Ratatouille-Whiskers/OpenWhisker/Code/TED_MLX90393/TED_MLX90393.ino

#include <MLX90393.h>
#include <Wire.h>

#define DRDY_pin 5

MLX90393 mlx;
MLX90393::txyzRaw rawData;
MLX90393::txyz data;

bool dataReady = false;

// Max reading rate is 385hz @ i2c_clk=100kHz (Teensy 4.0)
// Max reading rate is 320hz @ i2c_clk=100kHz (Esp32)
// Max reading rate is 570hz @ i2c_clk=400kHz (Teensy 4.0)
// Max reading rate is hz @ i2c_clk=400kHz (Esp32)
// const byte axisFlags = MLX90393::X_FLAG | MLX90393::Y_FLAG | MLX90393::Z_FLAG; 
// Removing the z-axis from the reading increases 385hz -> 460hz @ i2c_clk=100kHz (Teensy 4.0)
// Removing the z-axis from the reading increases 320hz -> hz @ i2c_clk=100kHz (Esp32)
// Removing the z-axis from the reading increases 570hz -> 680hz @ i2c_clk=400kHz (Teensy 4.0)
// Removing the z-axis from the reading increases hz -> hz @ i2c_clk=400kHz (Esp32)
const byte axisFlags = MLX90393::X_FLAG | MLX90393::Y_FLAG; 
// Removing the z-axis from the reading increases 460hz -> 578hz @ i2c_clk=100kHz (Teensy 4.0)
// Removing the z-axis from the reading increases hz -> hz @ i2c_clk=100kHz (Esp32)
// Removing the z-axis from the reading increases 680hz -> 870hz @ i2c_clk=400kHz (Teensy 4.0)
// Removing the z-axis from the reading increases hz -> 449hz @ i2c_clk=400kHz (Esp32)
// const byte axisFlags = MLX90393::Y_FLAG; 

void setup(){
    Serial.begin(115200);

    /* Wait for serial on USB platforms. */
    while (!Serial) {
        delay(10);
    }
    

    // disable the internal pullup resistors on the i2c pin as we use external pull-ups (in this case the one on the Sensor PCB)
    pinMode(SDA, INPUT);
    pinMode(SCL, INPUT);
    
    // Wire.setSDA(16); 
    // Wire.setSCL(17);
    
    // Wire.setClock(100000);
    Wire.setClock(400000); // setup for 400kHz on a teensy 4.0 resulted in 570Hz (all axis) being read form the sensor on the interrupts
    Wire.begin();
    // Wire.begin(0x18);
    // byte status = mlx.begin(0,0,5);
    byte status = mlx.begin(0, 0, DRDY_pin, Wire);
    attachInterrupt(DRDY_pin , mlxInterrupt, RISING);
    

    //Report status from configuration
    Serial.print("Start status: 0x");
    if(status < 0x10) Serial.print("0"); //Pretty output
    Serial.println(status, BIN);

    //set the hall configuration (for setting the hall plate spin phase, 2-Phase: 0xC, 4-Phase: 0x0)
    // mlx.setHallConf(0); // <=== NONE FUNCTIONING !!!

    mlx.setGainSel(1);
    mlx.setResolution(0, 0, 0); //x, y, z
    mlx.setOverSampling(0);
    mlx.setDigitalFiltering(0); 
    
    delay(100);

    Serial.println("Measurement Started");
    mlx.startBurst(
        axisFlags //set the flags for what we want to read 
    );

    //See MLX90393.h and .cpp for additional functions including:
    //set/getOverSample, set/getTemperatureOverSample, set/getDigitalFiltering, set/getResolution
    //set/getTemperatureCompensation, setOffsets, setWThresholds
}

int reads = 0;
unsigned long duration = micros();
unsigned long prev_time = micros();

void loop(){
    // mlx.readData(data); //Read the values from the sensor

    if (dataReady){
        // mlx.readData(data);

        mlx.readMeasurement(
            axisFlags, //set the flags for what we want to read 
            rawData // read the raw data
        );
        
        data = mlx.convertRaw(rawData);

        // reads++;
        // if(reads > 1000){
        //     duration = micros() - prev_time;
        //     Serial.print(duration);
        //     Serial.print(" ");
        //     Serial.print(reads);
        //     Serial.print(" | ");
        //     Serial.print("READ FREQ:");
        //     Serial.println(1000000.0/(float(duration)/reads));
        //     reads = 0;
        //     prev_time = micros();
        // }

        Serial.print(">X: "); Serial.println(data.x);
        Serial.print(">Y: "); Serial.println(data.y);
        Serial.print(">Z: "); Serial.println(data.z);

        dataReady = false;
        
        // mlx.startMeasurement(
        // axisFlags //set the flags for what we want to read 
        // );
    }
}

void mlxInterrupt(){
    dataReady = true;
}
